Jackief3/ECE445/Boards/New_PCB.jpg

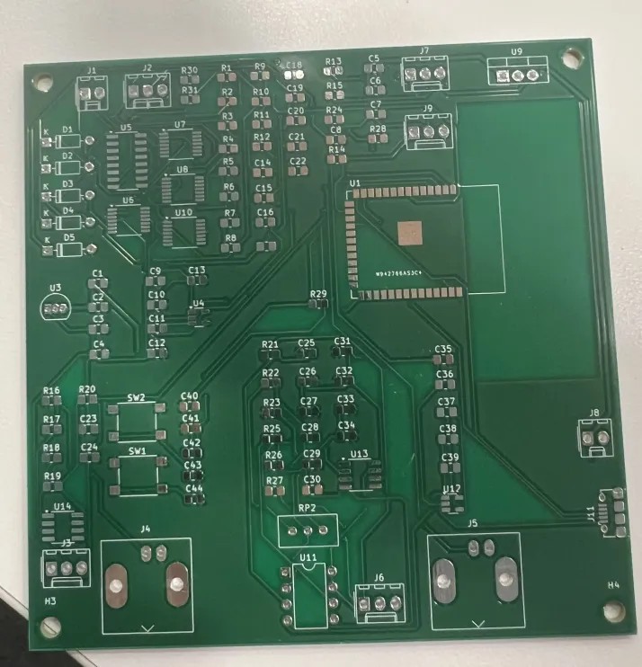
Boards/New_PCB.jpg
