Jackief3/ECE445/notebooks/jackie/Breadboard Demo2.jpg

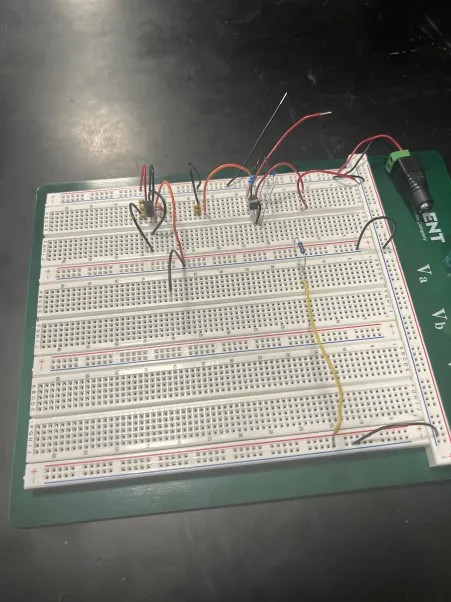
notebooks/jackie/Breadboard Demo2.jpg
