Jackief3/ECE445/notebooks/jackie/FinalPCB_HalfFinished.jpg

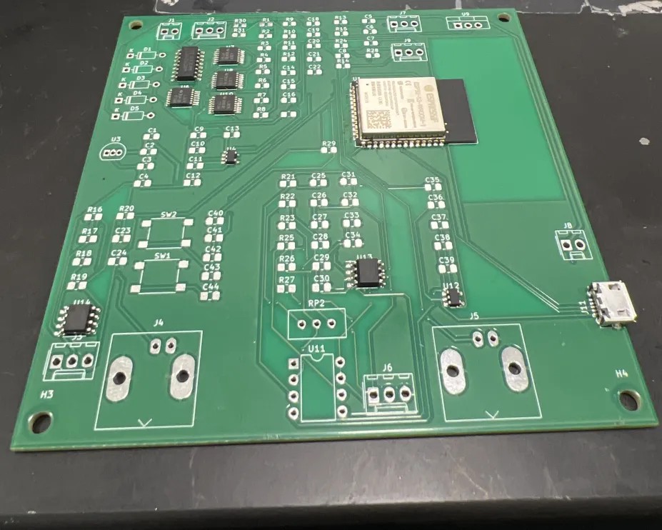
notebooks/jackie/FinalPCB_HalfFinished.jpg
