Jackief3/ECE445/notebooks/jackie/FinalPCB_MostlyFinished.jpg

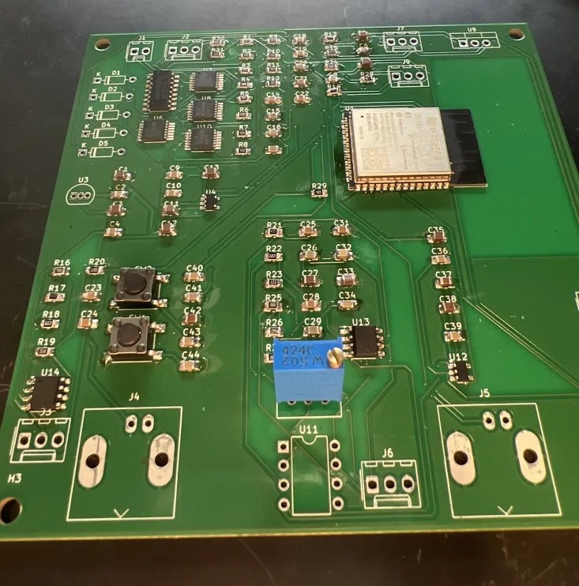
notebooks/jackie/FinalPCB_MostlyFinished.jpg
