Jackief3/ECE445/notebooks/jackie/SolderIssue.jpg

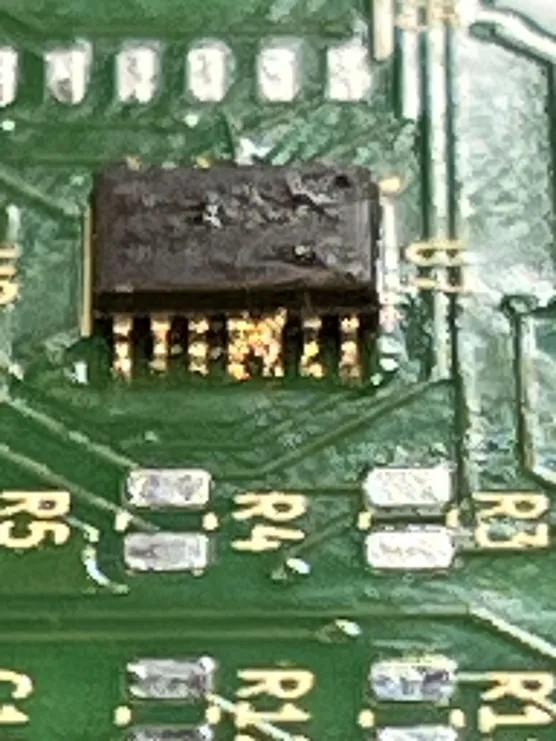
notebooks/jackie/SolderIssue.jpg
