Jackief3/ECE445/Results_3.jpg

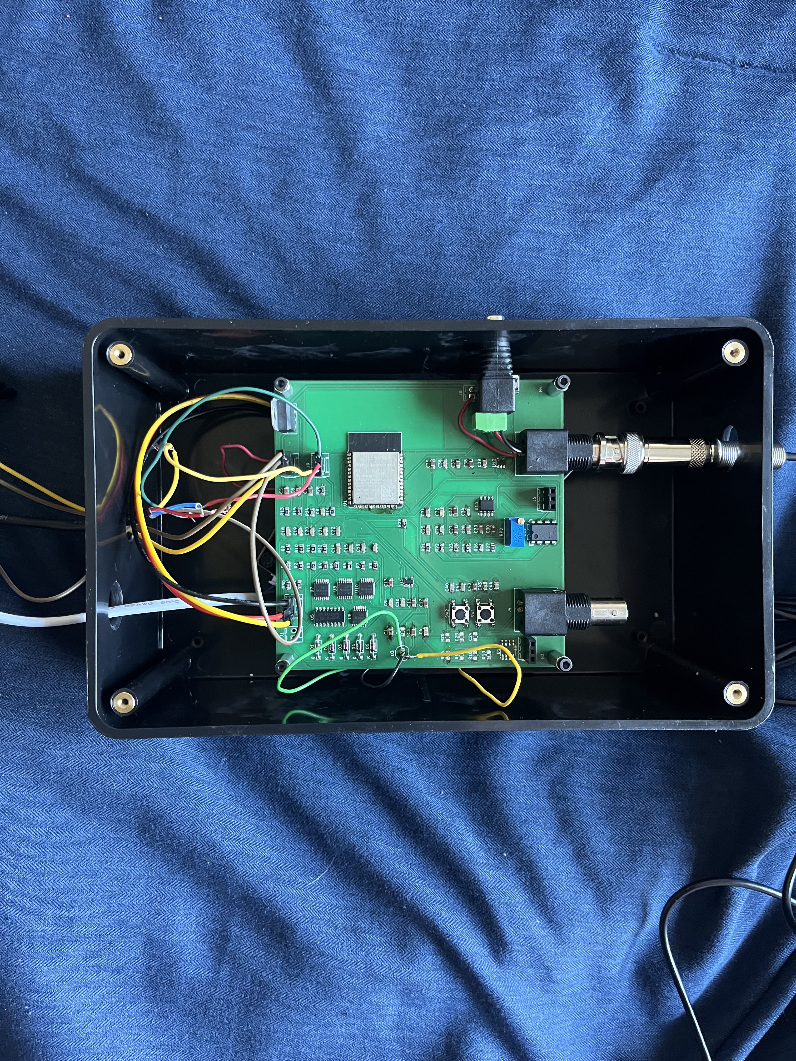
Results_3.jpg
